jacksonrwoodard/HouseHealthMonitoring/Reports/Conceptual Design & Planning/Conceptual_Design_Draft.pdf

# Conceptual Design

Jackson Woodard, Dylan Robbins, Nathaniel Campbell, Luke Carson, Cole Cooper
Electrical and Computer Engineering Department Tennessee Technological University Cookeville, Tennessee
jrwoodard44@tntech.edu, dcrobbins42@tntech.edu, nmcampbell43@tntech.edu, lmcarson43@tntech.edu, cacopper44@tntech.edu
I. INTRODUCTION

Houses face many types of issues like gas leaks, fires, floods, and mold, which cause damage to the house leading to a decrease in value [1]–[3]. Unlike a smartphone or a modern car, current house constructions lack a mechanism to detect and monitor this information. This information, such as knowing if water damage has occurred, could improve the value of the house by proving that issues have not occurred or were taken care of quickly by the homeowner. In order to detect and monitor all of these problems, this project proposes a collection of sensors and a head unit, called Preserve Home Pro. The goal of the system is to measure, record, and display important active and historical data, giving a homeowner valuable information to help maintain and protect the value of their home. The Preserve Home Pro will be designed as a semi-permanent system that will last for up to thirty years. The system will also communicate information through a closed network without requiring internet. Combining these concepts, this project proposes an advanced solution to house health monitoring.
A current market for this type of system does not exist. Although there are several devices available to detect specific problems, none of this technology is integrated as a single system in houses today. Since many homes face issues with gas leaks, fires, floods, and mold, actively detecting these issues could be beneficial in preserving a home’s value [1]–[3]. In summary, The Preserve Home Pro will be designed as a semi-permanent system with multiple sensor modules that would detect and log these threats to a house, potentially increasing the value of a home.
This document is important in the design process because it will present general solutions based on the specifications and constraints stated in the project proposal. The document will also explain what each subsystem will do and give a more detailed description of the subsystem as a whole. Expanding on each subsystem will give the team an easier understanding of the problem and the proposed solution.
A. Specifications & Constraints

Stated below is a full list of the shall statements for the project placed in number order to be referenced (SC#) later in the document.

1) The Head unit shall know what sensor is sending data to it, the sensor’s location, and be able to differentiate from other sensors. This originated from the team supervisor.
2) The Head unit shall be able to display and log active and historical data from sensors. This originated from the project team and team supervisor.
3) Head unit shall be able to detect if the fire module temperature is at 176 degrees Fahrenheit or higher and display a warning [4]. This originated from the project team based on the fact of the drywall ignition level.
4) The Head unit shall be able to receive data from the water module to display a warning if water is present and the total water depth. This originated from the project team.
5) Head unit shall receive data from the gas module and follow OSHA standards for ammonia, propane, and carbon oxides (50 ppm, 1000 ppm, and 50 ppm respectively over an eight-hour window) [5]. This originated from the OSHA standards for the project.
6) Head unit shall be able to interpret, from the received data, that mold could form if the humidity levels exceed 50% and temperatures range between 55 degrees and 85 degrees Fahrenheit for a minimum of two days [6]. This originated from the project team based on the conditions in which mold can grow.
7) Head unit shall be able to receive the sensor name, number, data type, and raw data. This originated from the team supervisor.
8) Shall be a semi-permanent system that will last for up to thirty years. This originated from the team supervisor.
9) Shall have a backup power system that will allow the system to function in case of a primary power outage for up to two continuous weeks. This originated from both a standard and the team supervisor.
10) Shall fully function without having to regularly change batteries in sensors or head unit. This originated from all external stakeholders and the team supervisor.
11) Sensor modules shall not be placed in a way where they cannot wirelessly communicate with the system. This originated from the project team and broader implications.
12) Modules shall not be a distraction for a homeowner, and not be directly visible. This originated from all external stakeholders and the team supervisor.

13) The Water module shall be able to detect multiple water levels and determine if water is present. This originated from the project team.
14) The Mold module shall be able to detect the current temperatures and humidity levels in an area and send it to the head unit. This originated from the project team.
15) The Gas module shall be able to detect ammonia, propane, and carbon oxide. This originated from the project team and the insurance companies.
16) The Fire module shall be able to detect the temperature of the sensor and send the data to the head unit. This originated from the project team.
17) System shall not require an internet connection to work and communicate with the head unit and sensors. This originated from homeowners, insurance agencies, and the team supervisor.
18) Sensor communication shall send the sensor name, number, data type, and raw data to the head unit. This originated from the project team.
19) System shall not collect additional data that is not required for sensor functionality. This originated from all internal and external stakeholders and from broader implications.
20) System shall follow all IEEE Code of Ethics and common standards. This originated from the IEEE Code of Ethics.
B. Ethics & Broader Considerations
The design team will follow all National Fire Protection Agency 70: National Electrical Code (NFPA 70) and Occupational Safety and Health Administration (OSHA) procedures [SC5]. The team will also follow all government laws stated by the United States of America Government. The team will also follow all IEEE Code of Ethics and common standards, like resistor color codes, communications between devices, and design schematics [SC20]. The team will legally use all copyrights, patents, and licenses when necessary. The system will be designed to prevent all risk and harm when operated by the user and not be a distraction [SC12].

Due to the limited time and budget allocated to this project, there are multiple broader implications. Broader implications are the potential effects that the system could cause. Firstly, it may interfere with nearby radio frequency devices. Secondly, there is a risk of fire if any of the backup batteries become damaged. Additionally, false positives may be triggered due to sensor wear or damage. Also, one concern from the stakeholders is unnecessary data recording and sharing. It is essential that the system will not record conversations or cause any insecurities to the user [SC19]. Finally, given the installation process, it may be difficult to determine the level of effort required to maintain the sensors.

II. BLOCK DIAGRAM

The full detailed block diagram is pictured at the end of the document in figure 10.

A. Power System

The power system allows the Preserve Home Pro modules to function primarily on power from the house with a secondary backup battery in case of outages [SC9]. An uninterruptible power supply (UPS) will need to be implemented to allow the sensor modules to remain connected to the head unit. A charging system for the battery will also be needed so users do not have to change out batteries [SC10]. This power system will allow the Preserve Home Pro to operate for up to 30 years [SC8].


Fig. 1. Block Diagram of the Power System

B. Communication System

The Preserve Home Pro system uses wireless communication without an existing internet or WiFi connection in the house[SC17]. The transmission of the information from each module is used to record specific conditions of the house whether mold has grown, if water has accumulated, if gas is leaking or if a fire has occurred. Preserve Home Pro needs to be able to transmit the information from each module[SC11]. The information transmitted from each module should include the name of the sensor, the number of the sensor, the data type, and the sensor information[SC18]. The sent information should be small enough in data size to allow for minimal to no processing from the modules. The sent information should also allow for the head unit to discern each module from the others to allow for data processing of multiple inputs.

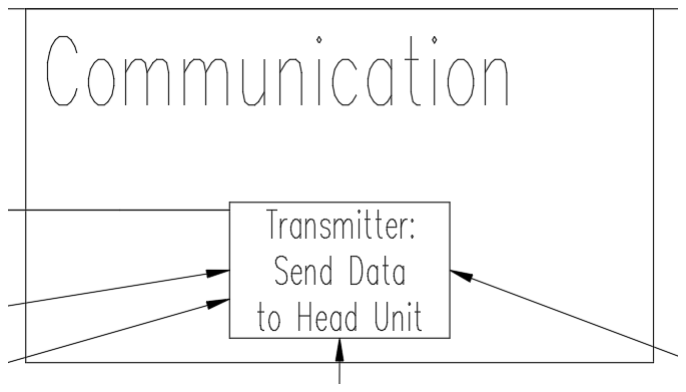
[picture p21: figure]

Fig. 2. Block Diagram for Communication System Transmitter

The head unit needs to be able to communicate with each of the modules. The reception of the information from each module is necessary for the proper functionality of the system. The received information will be routed through a receiver in the head unit. This receiver will be able to take information from the modules, like the name of the sensor, the sensor number, the data type, and the sensor information[SC1]. The information received can be used to determine if damage from mold, fire, water, or gas has occurred, and where the damages have occurred.

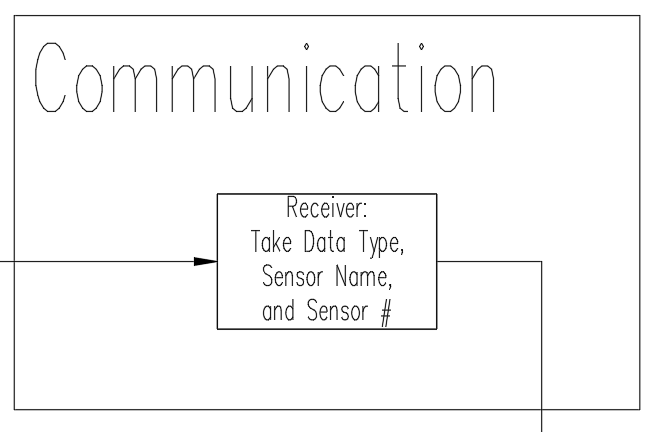
[picture p22: figure]

Fig. 3. Block Diagram for Communication System Receiver

C. System Modules
1) Head Unit: The head unit will be designed to display active and historical data [SC2]. The head unit will be able to determine the sensor name, number, data type, and raw data [SC7]. This information will be organized and interpreted to know what sensor is sending the data, and the sensor’s location, and be able to differentiate from other sensors [SC1]. The head unit will be able to detect if a temperature sensor has a temperature of 176 degrees Fahrenheit or higher and display a warning to the user [SC3]. It will also be able to detect if a water sensor has water present and the total depth of the water [SC4]. The head unit will also be able to determine if the data from the gas sensors are in the specified range according to OSHA standards for a set period of time [SC5]. Finally, the head unit will be able to determine if the data from the mold module is in the specified ranges for humidity and temperature and display a warning for potential mold growth if the conditions are present for a minimum of two days [SC6].

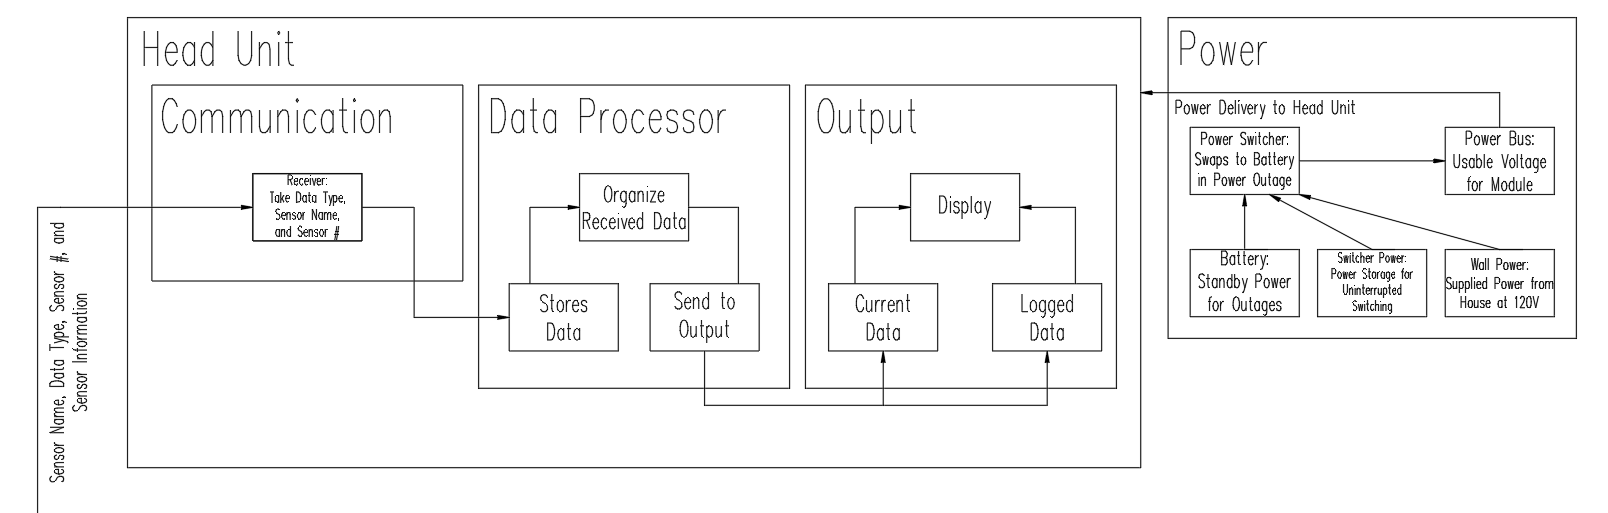
[picture p23: figure]

Fig. 4. Block Diagram of Head Unit

2) Mold Module: The mold module will be designed to have humidity and temperature sensors detecting their respective levels in a specified area and send the raw data, in the form of real numbers, back to the head unit [SC14]. These sensors will work together to determine if mold is likely to grow within the specified area. With the data the head unit receives from each sensor, the head unit will trigger a warning for potential mold growth if humidity levels exceed 50% and temperatures range between 55 to 85 degrees Fahrenheit for a minimum of two days [SC6].

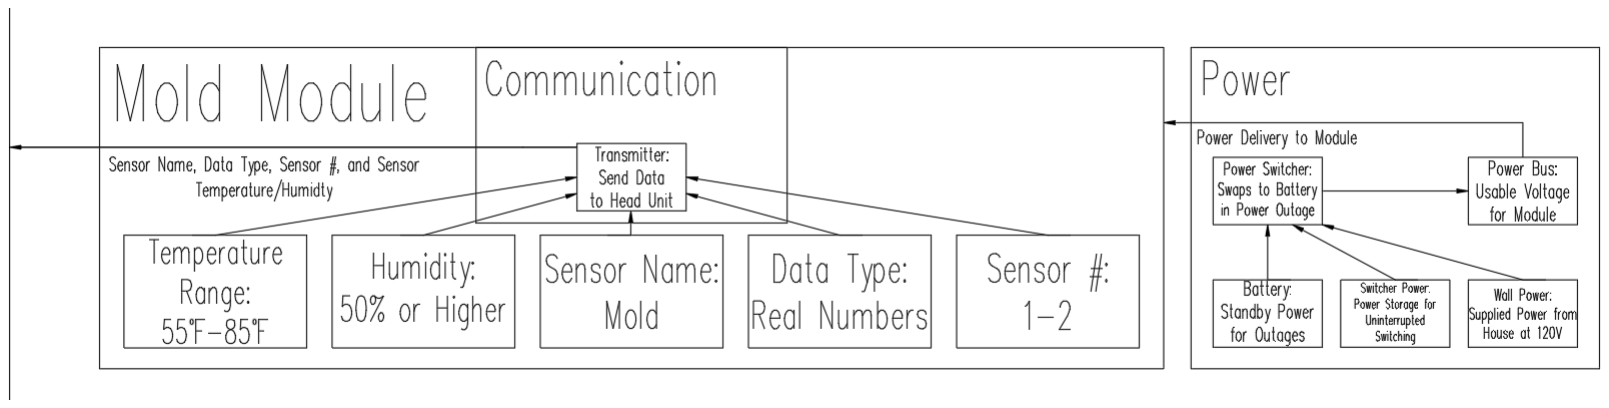
[picture p24: figure]

Fig. 5. Block Diagram of Mold Module

3) Gas Module: The gas module will detect three distinct gases – ammonia, carbon oxides, and propane - that tend to overlap in different sections of the house, such as smoke, septic, and natural gases [SC15]. The module is designed to detect these gases in specific areas of the house that are prone to leaks. Once the module detects the gases, built around OSHA standards, the data will be sent to the head unit for diagnosis [SC5].

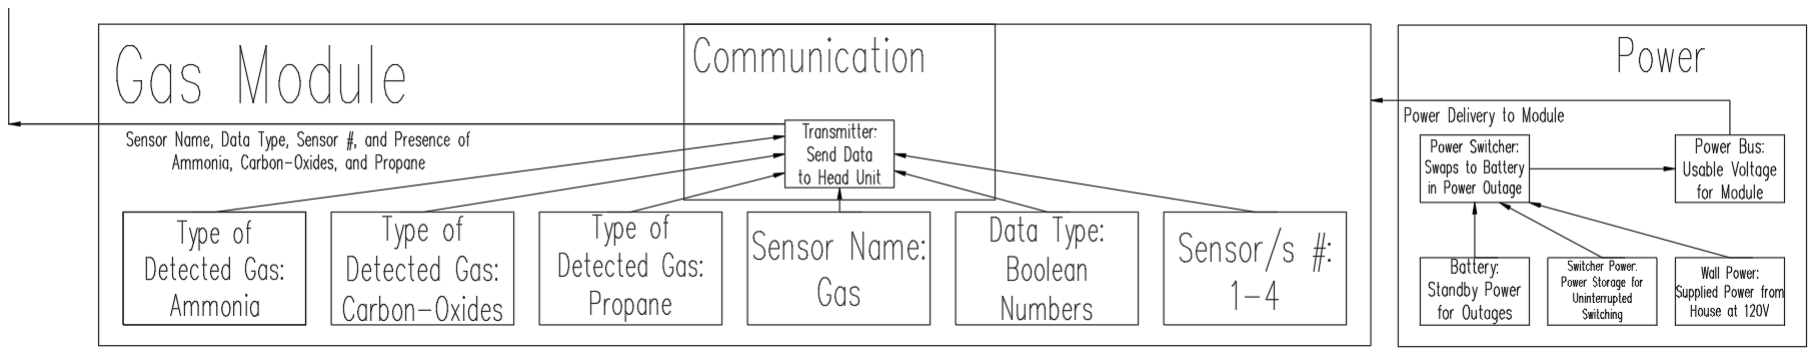
[picture p25: figure]

Fig. 6. Block Diagram of Gas Module

4) Fire Module: The fire module will be designed with sensors that will detect the current temperature and send the temperature data in the form of real numbers back to the head unit [SC16]. Once the data is received by the head unit, it will determine if the temperature is 176 degrees Fahrenheit or higher and display a warning message for the user to see [SC3].

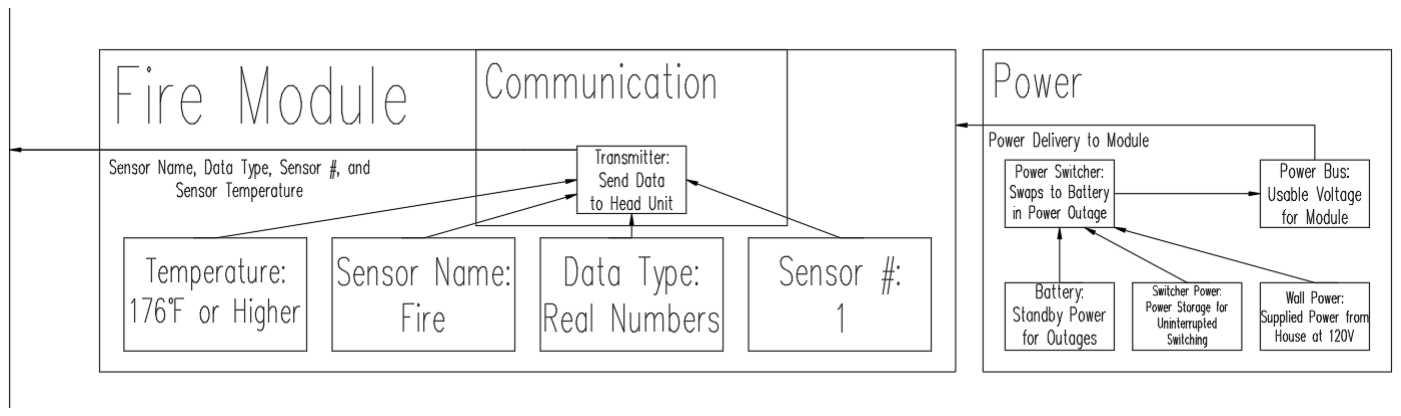
[picture p26: figure]

Fig. 7. Block Diagram of Fire Module

5) Water Module: The water module will have a sensor that can detect if water is present and the total depth of water[SC13]. It will then send this information back in the forms of real and Boolean values to the head unit so it can interpret and display the data [SC4].

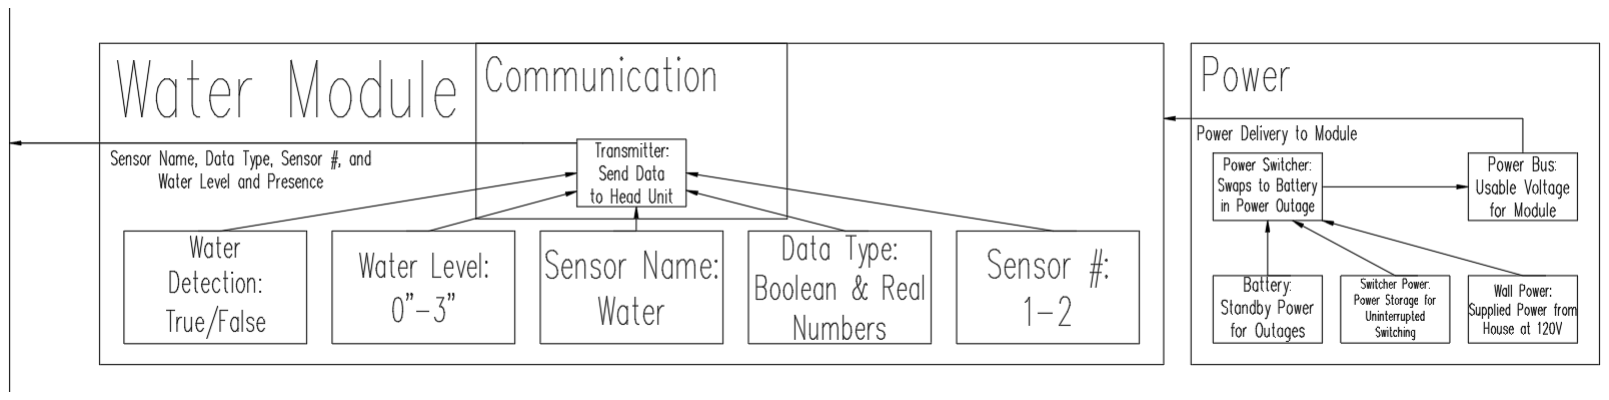
[picture p27: figure]

Fig. 8. Block Diagram of Water Module

III. TIMELINE
The expected timeline for the project is around one year. Figure 9 displays a Gantt chart that shows all of the team’s expected completion dates. The team plans to have everything built, utilized, and tested by May of 2024.

IV. CONCLUSION
In conclusion, the Preserve Home Pro project presents a solution to address various home health risks that can cause damage and deplete the value of a home such as gas leaks, fires, floods, and mold growth. The system will consist of multiple sensors and a head unit that will measure, record, and display historical and real-time data, providing homeowners with valuable information to help maintain and protect their homes. Each system module will be integrated into a semi-permanent system with a potential lifespan of up to thirty years. No internet connection will be required as the system will run within a closed network. This system is aimed to potentially help increase property value as well as give homeowners peace of mind that their home will remain in good health. This document serves as a foundational resource for the project, offering solutions aligned with project specifications and constraints and providing a detailed understanding of each subsystem’s role, marking a significant step towards revolutionizing home protection and preservation.

REFERENCES

[1] Insurance Information Institute, “Facts + statistics: Homeowners
and | renters | insurance,” | III, | https://www.iii.org/fact-statistic/
facts-statistics-homeowners-and-renters-insurance#:∼:text=In% 202021%2C%205.3%20percent%20of%20insured%20homes% 20experienced%20a%20claim,with%206.3%20percent%20in% 202020(accessedSep.17,2023).
[2] R. Peysakhovich, “47 mold statistics: Black Mold deaths per year,” Professional Commercial Cleaning Services by Onedesk, https://www.getonedesk.com/mold-statistics (accessed Sep. 17, 2023).
[3] M. Ahrens, Fire safety in the United States since 1980 - NFPA, https://www.nfpa.org/∼/media/Files/News%20and%20Research/Fire%20statistics%20and%20reports/US%20Fire%20Problem/
osNFPAEcosystemFireSafetyReport2021.ashx | (accessed | Sep. | 17,
2023).
[4] N. P. Team, “At what temperature will drywall ignite?,” NCERT POINT, https://www.ncertpoint.com/2022/01/at-what-temperature-willdrywall-ignite.html (accessed Oct. 3, 2023).
[5] OSHA, | “1910.1000 | table | Z-1 | - | Table | Z-1 | lim-
its | for | Air | Contaminants,” | Occupational | Safety | and
Health | Administration, | https://www.osha.gov/laws-
regs/regulations/standardnumber/1910/1910.1000TABLEZ1 | (accessed
Oct. 3, 2023).
[6] Adam, “Mold Chart for Temperature and Humidity Monitors,” Stetten home services, https://energyhandyman.com/knowledge-library/moldchart-for-temperature-and-humidity-monitors/ (accessed Sep. 28, 2023).

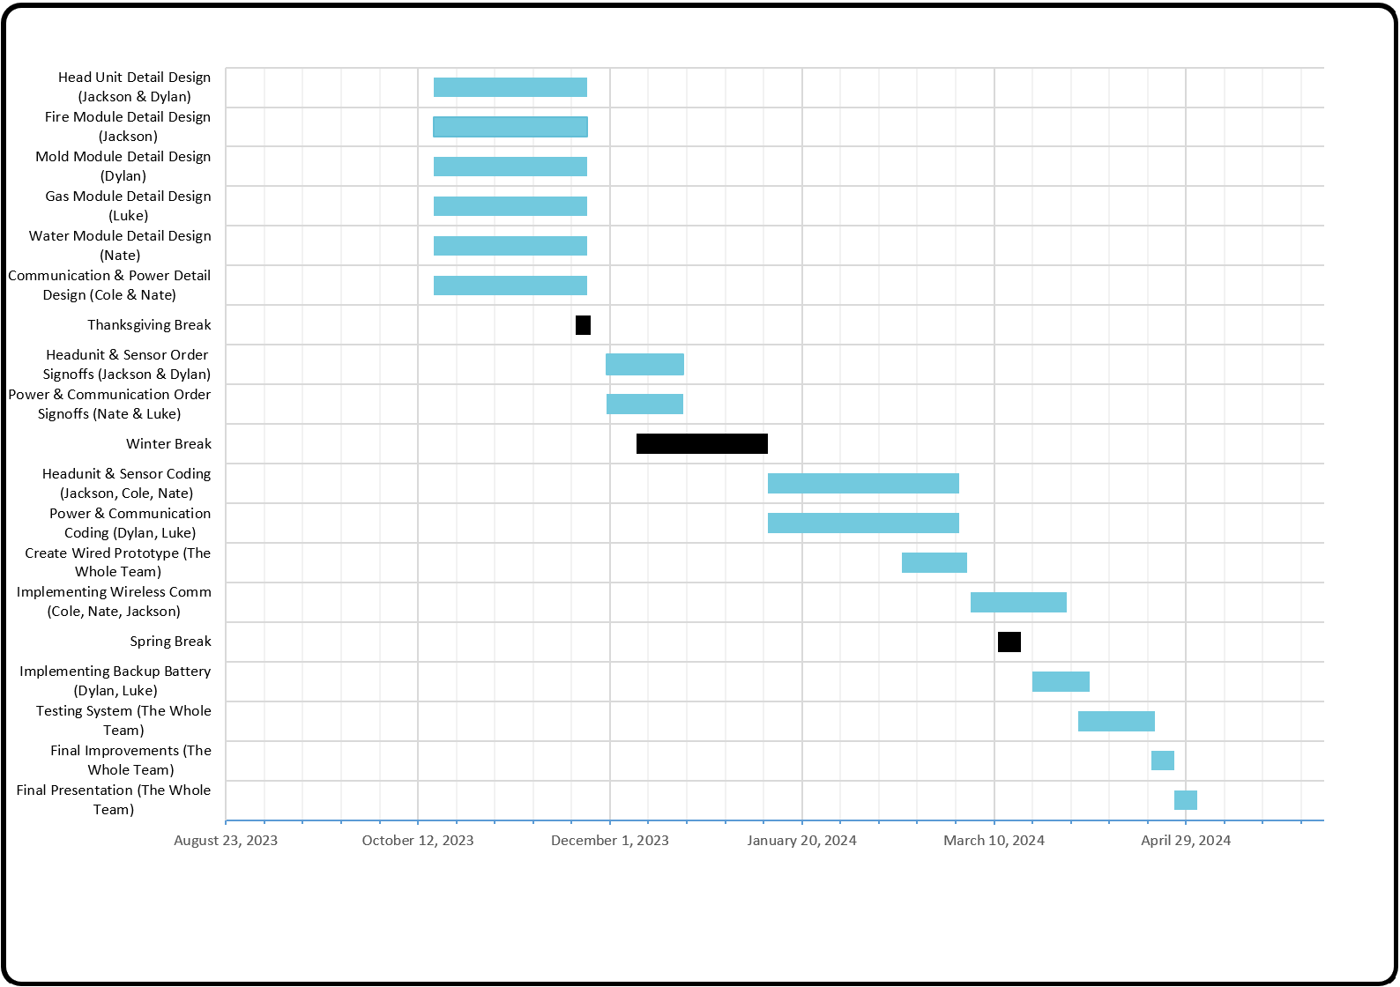
[picture p28: figure]

Fig. 9. Expected Timeline

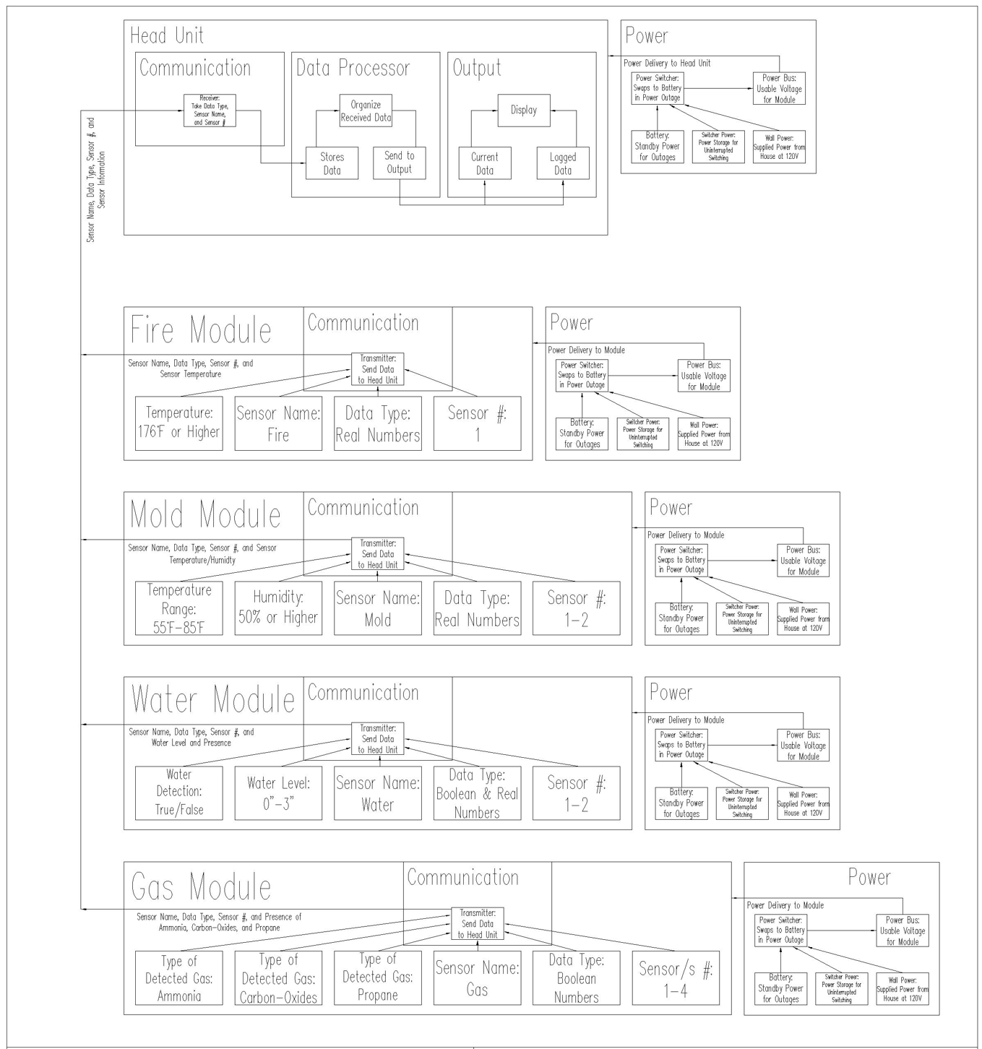
[picture p29: figure]

Fig. 10. Detailed Block Diagram
