jacksonrwoodard/HouseHealthMonitoring/Documentation/Meeting Minutes/Minutes - 2023-10-12.md

Opening
The team meeting of Capstone I Team 4 was held at 12:00 PM on October 12, 2023 in Brown Hall in room 408.

Present
Nate Campbell, Team Member
Luke Carson, Team Member
Cole Cooper, Secretary
Dylan Robbins, Team Member
Jackson Woodard, Team Lead
Jesse Roberts, Sponsor

Absent
All Present

Approval of Agenda
The agenda was unanimously approved by the team.

Approval of Minutes
The meeting minutes were unanimously approved by the team.

Business From Previous Meeting
The final edits of the project proposal corrections and the initial conceptual design submission.

New Business 
No new business was started from this meeting. 

Additions to the Agenda
Additional information for the specifications and constraints is needed before the project proposal’s submission. 
Extra text for the flow chart’s arrows for ease of reading also needs to be added. 
Some small clarifications on how the flow chart works in the paper was requested, 
however the request came from a skimming of the paper and the team feels that this request has been met. 

Agenda for Next Meeting
Initial planning for the detailed design submissions. 

Adjournment 
Meeting was adjourned at 3:00 PM by Jackson Woodard. With planning of meeting again on October 19, 2023 at 12:00 PM in Brown 408.

Minutes Submitted by: Cole Cooper
Approved by: Jackson Woodard
