jacksonrwoodard/HouseHealthMonitoring/Documentation/Meeting Minutes/Minutes - 2023-10-5.md

Opening
The team meeting of Capstone I Team 4 was held at 12:00 PM on October 5, 2023 in
Brown Hall in room 408.
Present
Nate Campbell, Team Member
Luke Carson, Team Member
Cole Cooper, Secretary
Dylan Robbins, Team Member
Jackson Woodard, Team Lead
Jesse Roberts, Sponsor
Absent
All Present
Approval of Agenda
The agenda was unanimously approved by the team.
Approval of Minutes
The meeting minutes were unanimously approved by the team.
Business From Previous Meeting
Editing of the flow chart, conceptual design paper, and project proposal were done
during this meeting.
New Business
No new business was started from this meeting.
Additions to the Agenda
A decent amount of discussion around making sure the project proposal follows the
supplied rubric was done. We ended up dividing the workload between each member in
order to speed up the editing process. After each individual section was completed, the
team went through and reviewed the edited information to ensure the goals of the rubric
were properly met this time around. This process was then repeated for the conceptual
design and the conceptual design block diagram.
Agenda for Next Meeting
Final edits for the conceptual design and block diagram will be covered next meeting.
Adjournment
Meeting was adjourned at 3:00 PM by Jackson Woodard. With planning of meeting
again on October 12, 2023 at 12:00 PM.
Minutes Submitted by: Cole Cooper
Approved by: Jackson Woodard
