jacksonrwoodard/HouseHealthMonitoring/Documentation/Electrical/Schematics/Sources/Communication.pdf

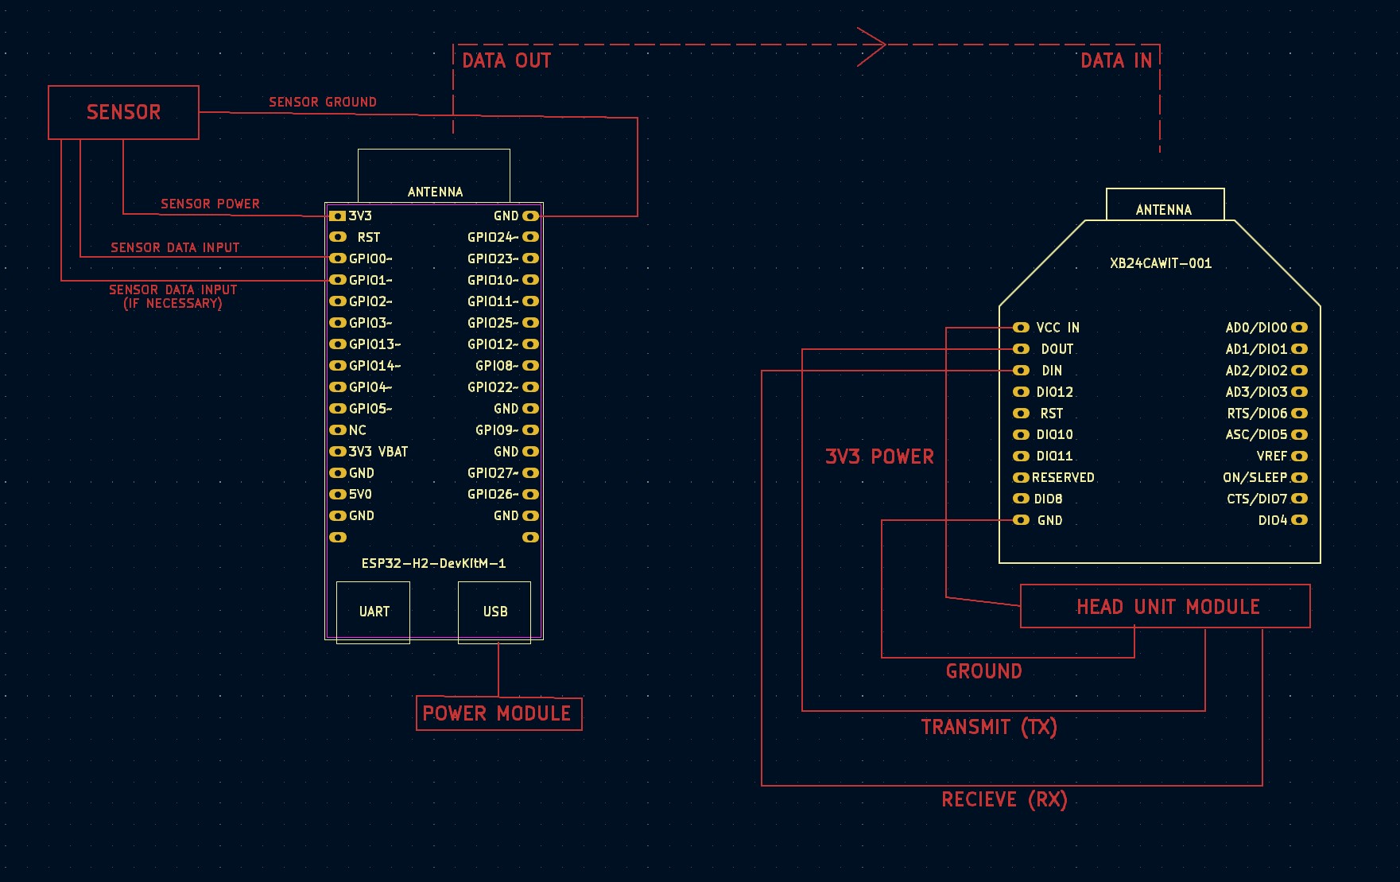
[picture p30: page 1]
