jacksonrwoodard/HouseHealthMonitoring/Documentation/Electrical/Schematics/Sources/Fire.pdf

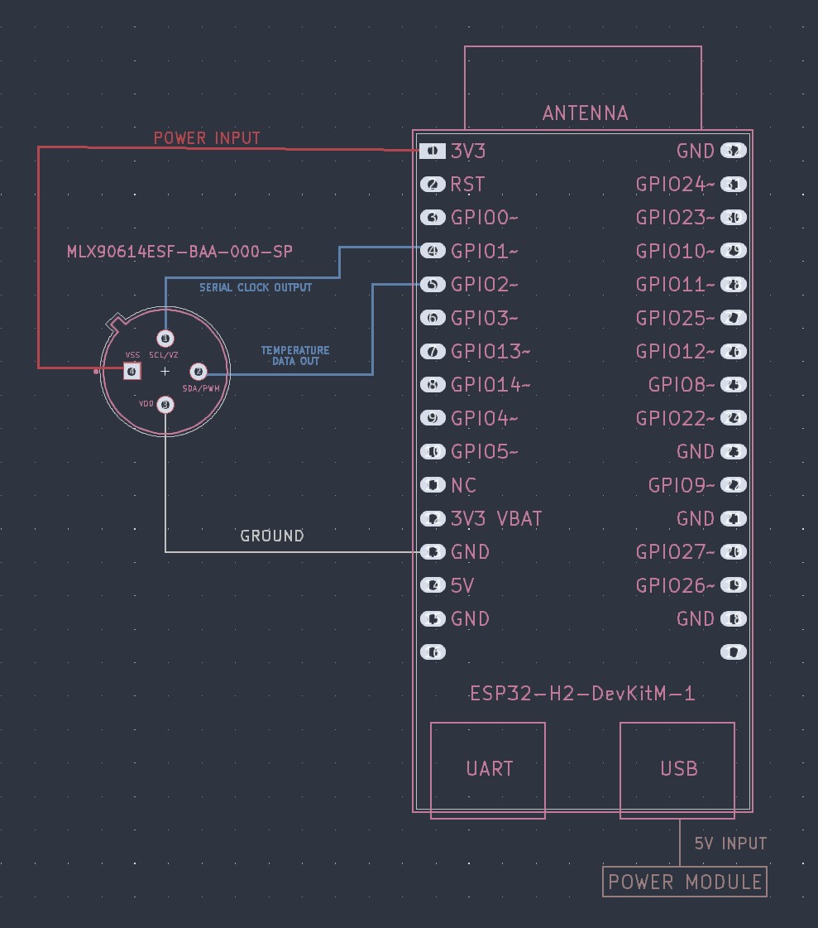
[picture p31: page 1]
