jacksonrwoodard/HouseHealthMonitoring/Documentation/Electrical/Schematics/Sources/Flood.pdf

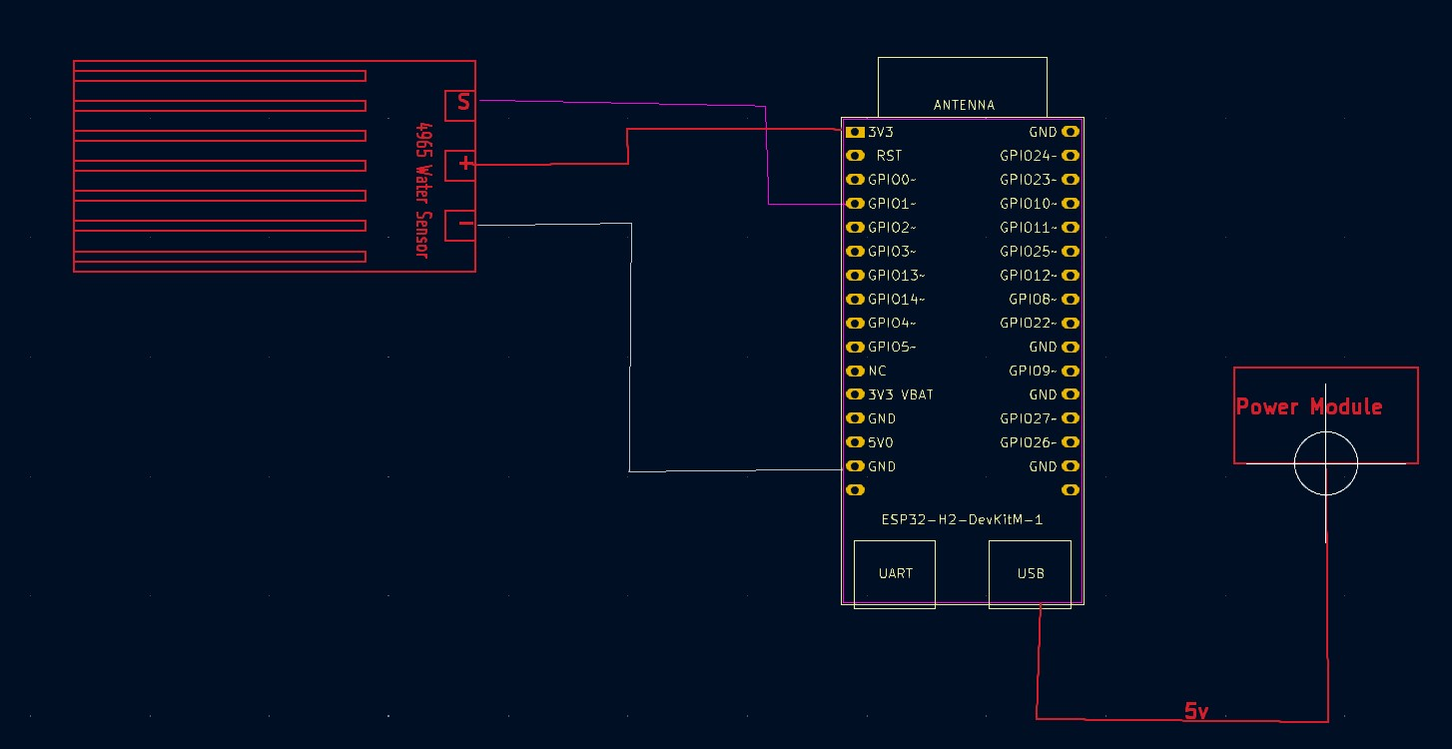
[picture p32: page 1]
