jacksonrwoodard/HouseHealthMonitoring/Documentation/Electrical/Schematics/Sources/Gas.pdf

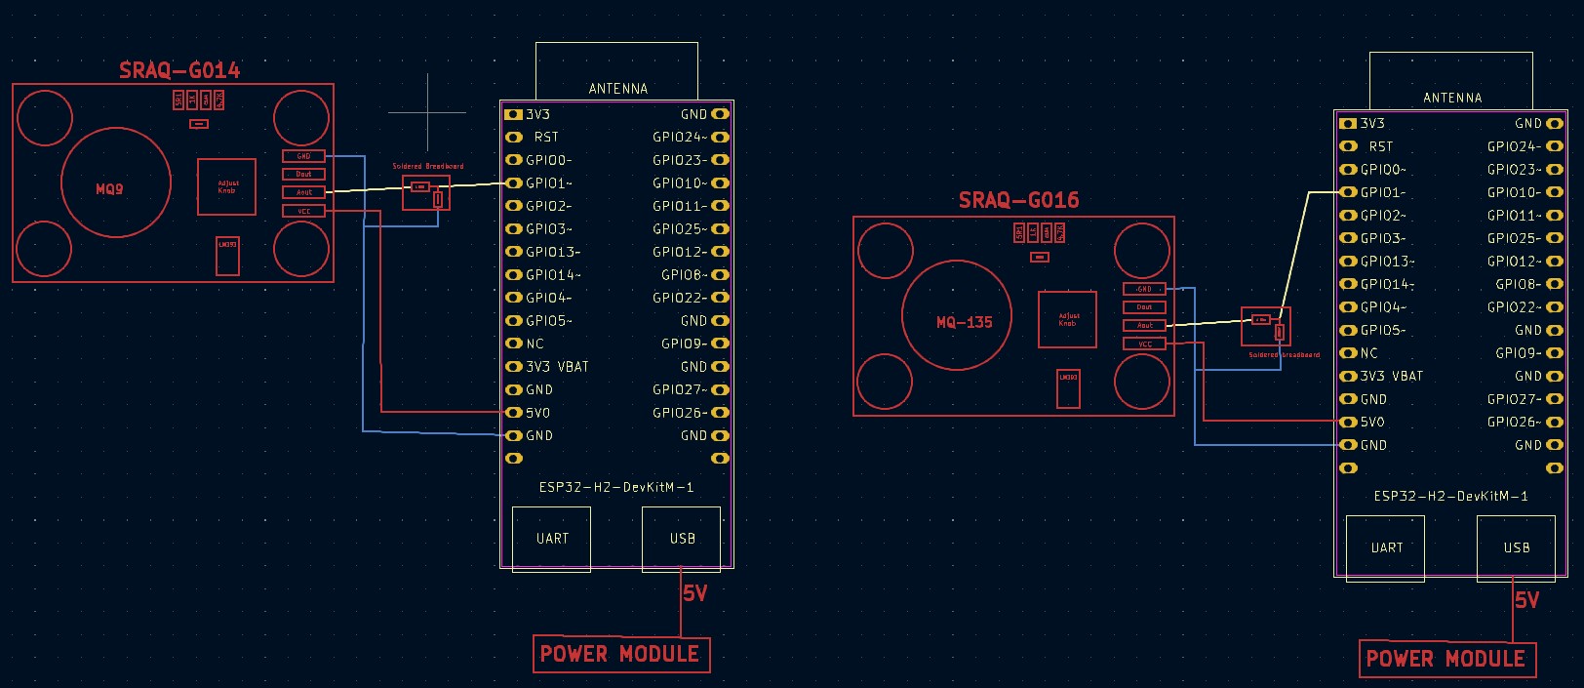
[picture p33: figure]
