jacksonrwoodard/HouseHealthMonitoring/Documentation/Electrical/Schematics/Sources/Head_Unit.pdf

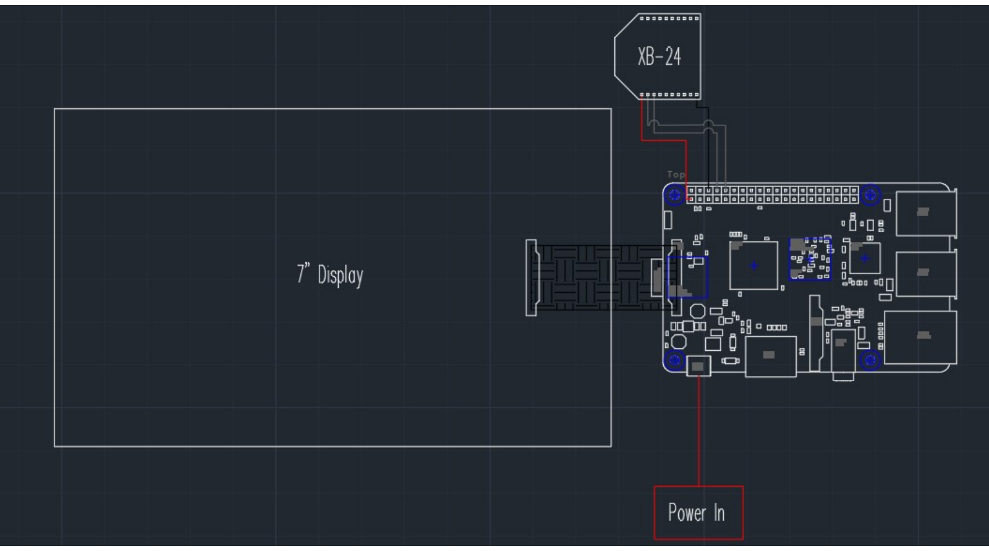
[picture p34: page 1]
