jacksonrwoodard/HouseHealthMonitoring/Documentation/Electrical/Schematics/Sources/Mold.pdf

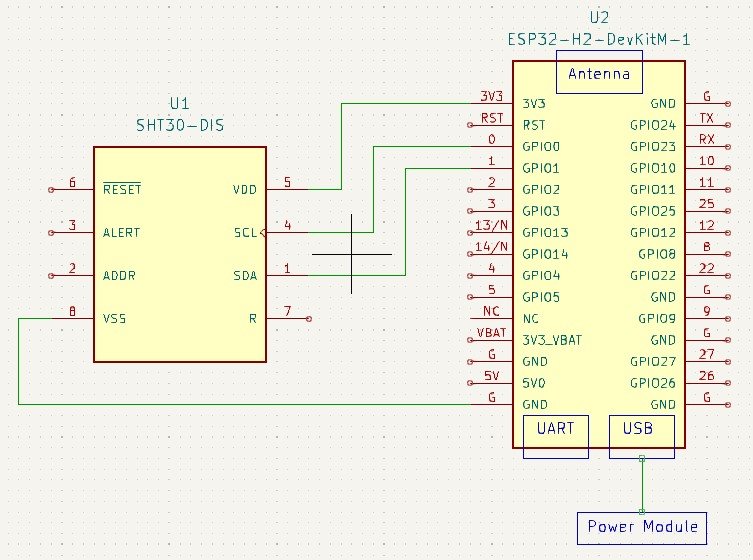
[picture p35: figure]
