jacksonrwoodard/HouseHealthMonitoring/Documentation/Electrical/Schematics/Sources/Power.pdf

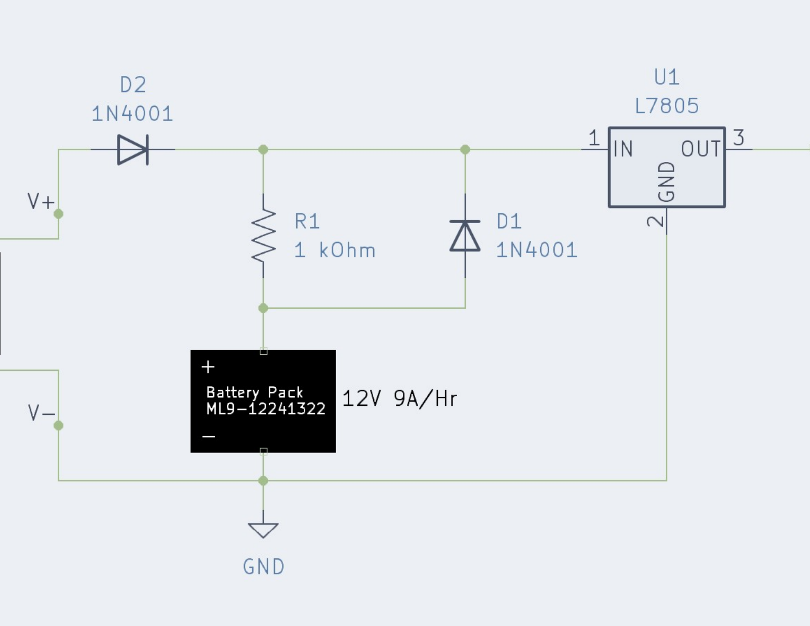
[picture p36: page 1]
