jacksonrwoodard/HouseHealthMonitoring/Documentation/Images/Communication/Reciever.png

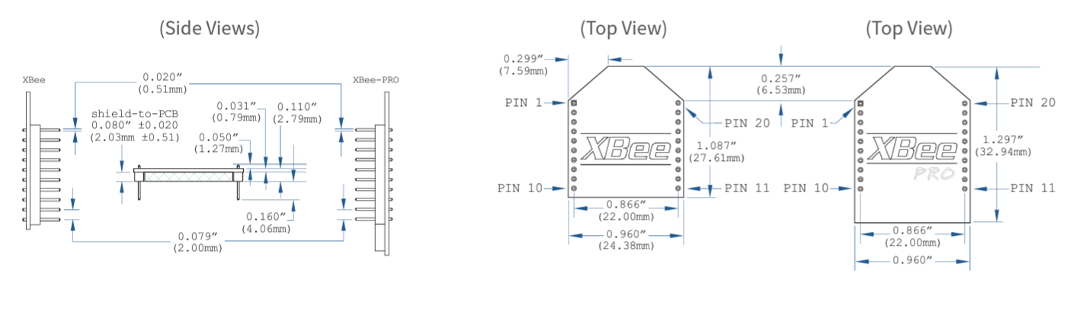
Documentation/Images/Communication/Reciever.png
