jacksonrwoodard/HouseHealthMonitoring/Documentation/Images/HeadUnit/Head_Unit_Display.PNG

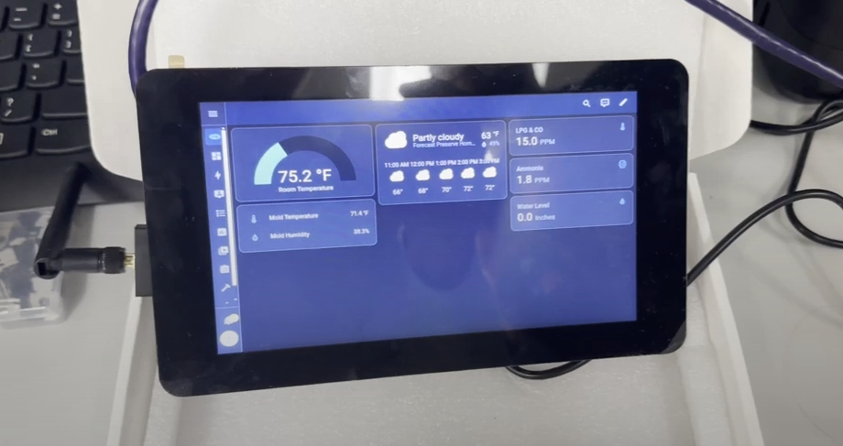
Documentation/Images/HeadUnit/Head_Unit_Display.PNG
