jacksonrwoodard/HouseHealthMonitoring/Documentation/Images/HeadUnit/Head_Unit_MCU.PNG

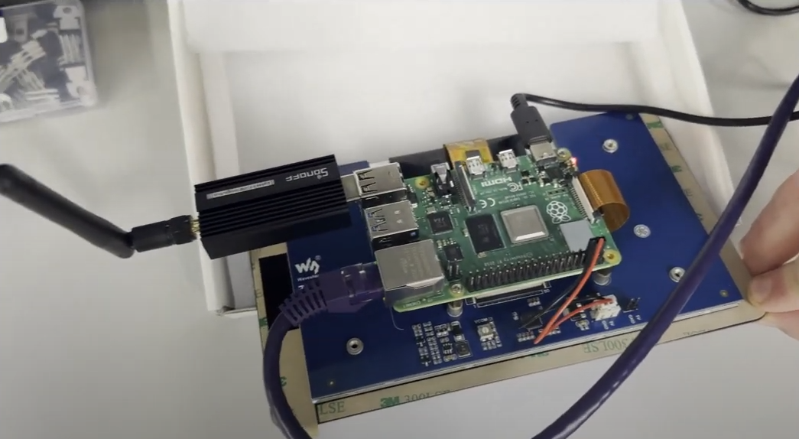
Documentation/Images/HeadUnit/Head_Unit_MCU.PNG
