jacksonrwoodard/HouseHealthMonitoring/Documentation/Images/Mold/Mold_Sensor.jpg

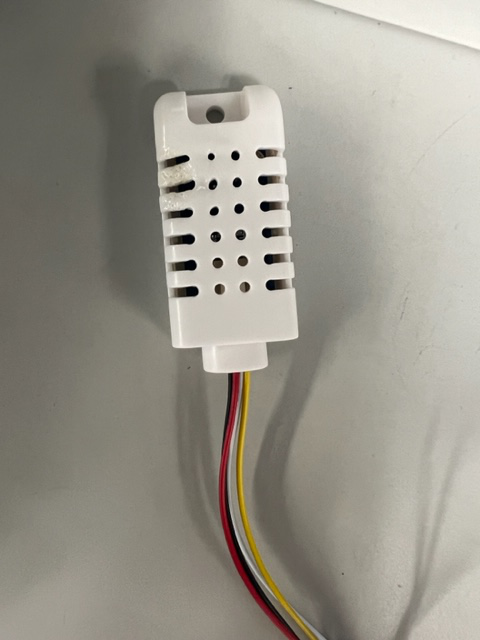
Documentation/Images/Mold/Mold_Sensor.jpg
