jacksonrwoodard/HouseHealthMonitoring/Documentation/Images/Communication/Communication_Test_50ft.png

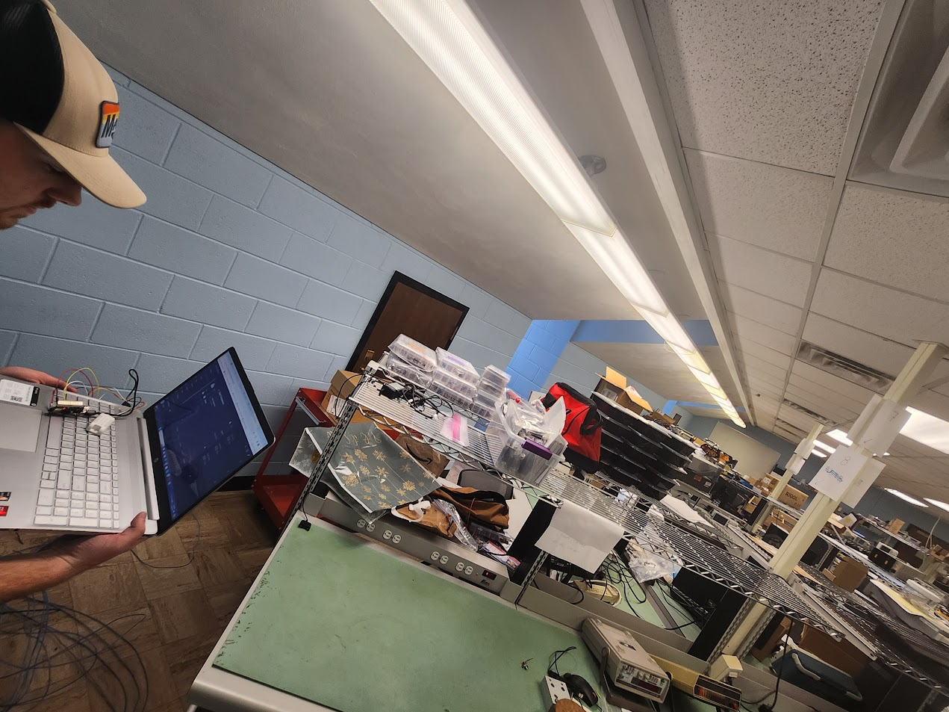
Documentation/Images/Communication/Communication_Test_50ft.png
