jacksonrwoodard/HouseHealthMonitoring/Documentation/Images/Communication/Communication_Test_100ft_with_walls.png

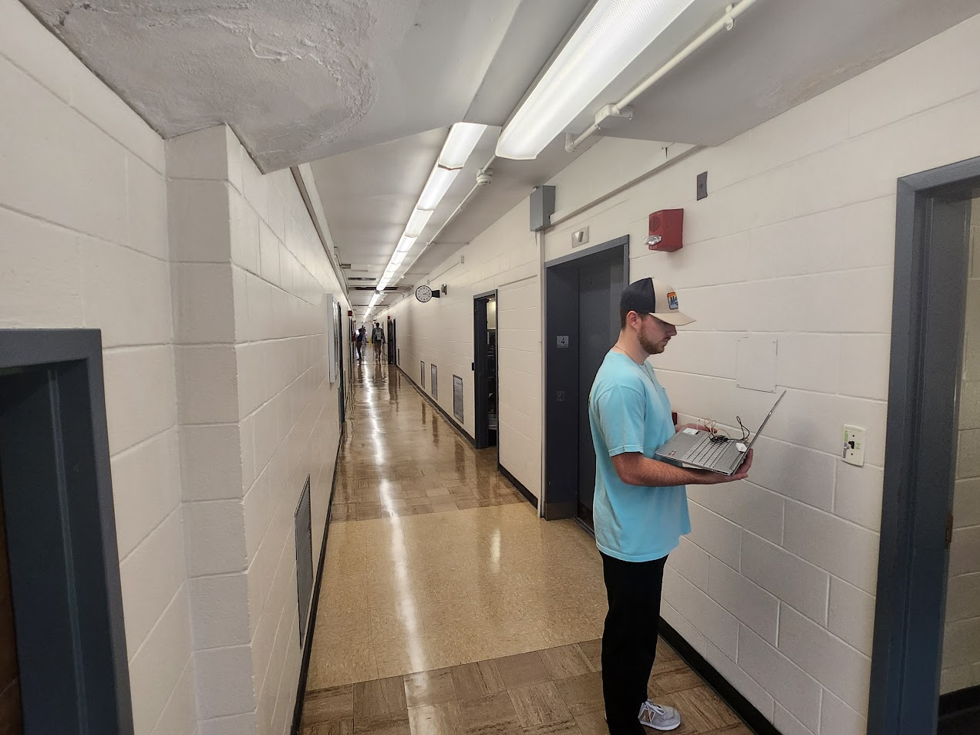
Documentation/Images/Communication/Communication_Test_100ft_with_walls.png
