jacksonrwoodard/HouseHealthMonitoring/Documentation/Images/Fire/Fire_Test_176_Degree.jpg

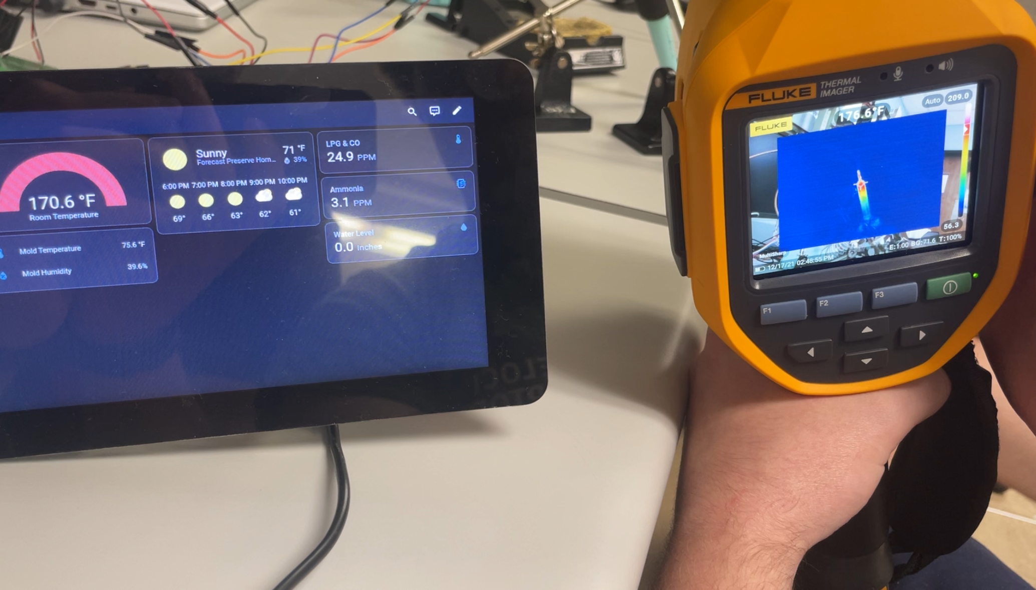
Documentation/Images/Fire/Fire_Test_176_Degree.jpg
