jacksonrwoodard/HouseHealthMonitoring/Documentation/Images/Gas/Gas_Test_Airvent.png

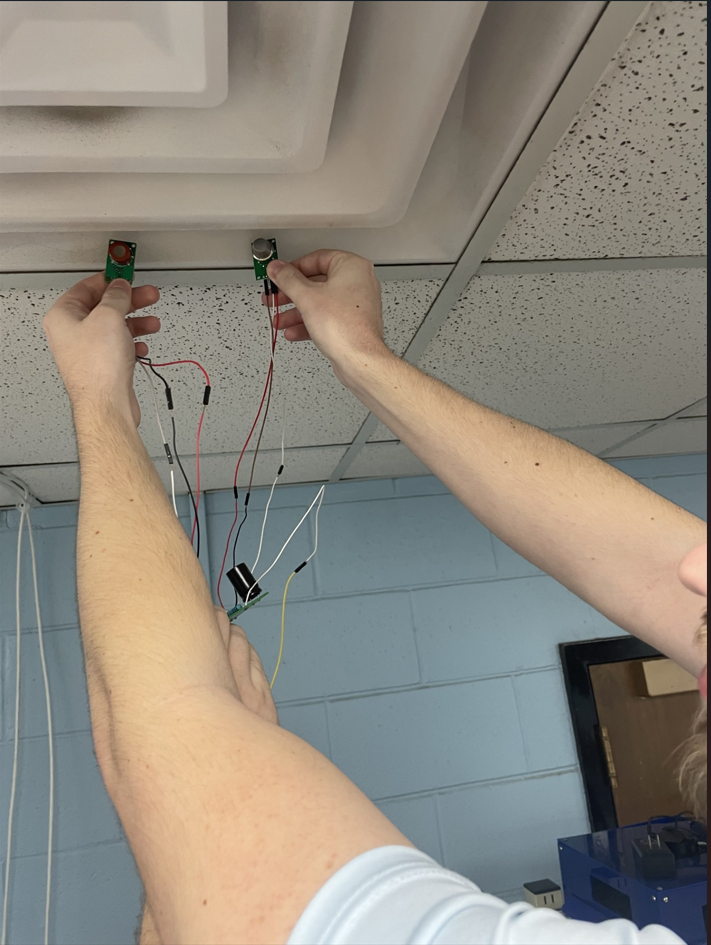
Documentation/Images/Gas/Gas_Test_Airvent.png
