jacksonrwoodard/HouseHealthMonitoring/Documentation/Images/Gas/Gas_Test_Dust.png

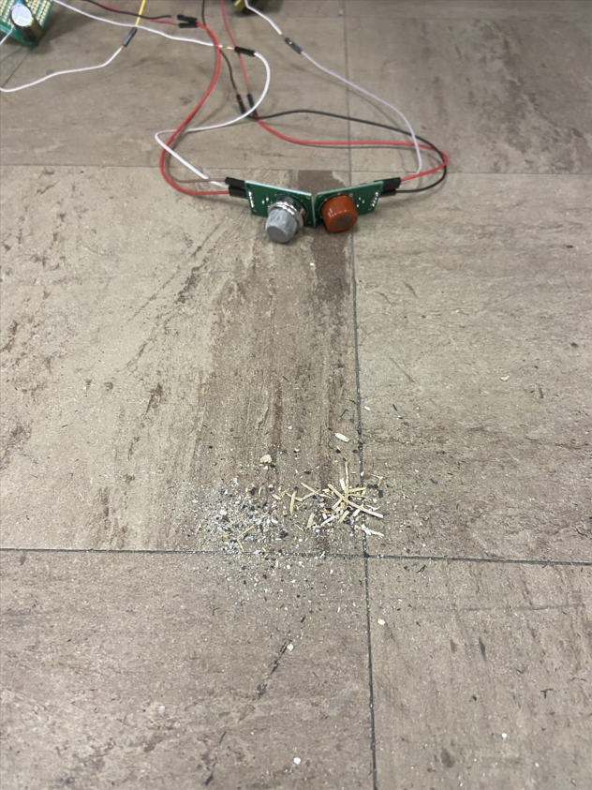
Documentation/Images/Gas/Gas_Test_Dust.png
