jacksonrwoodard/HouseHealthMonitoring/Documentation/Images/Power/Power_Plugged_In_Test.png

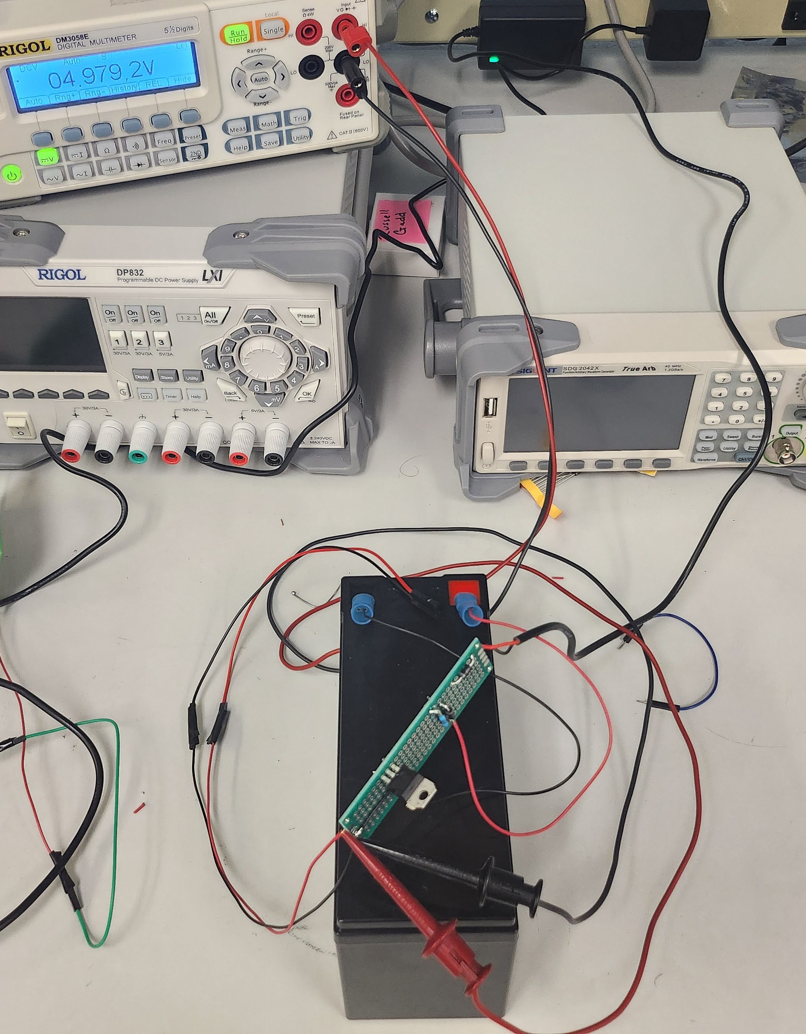
Documentation/Images/Power/Power_Plugged_In_Test.png
