jacksonrwoodard/HouseHealthMonitoring/Documentation/Images/Power/Power_Unplugged_Test.png

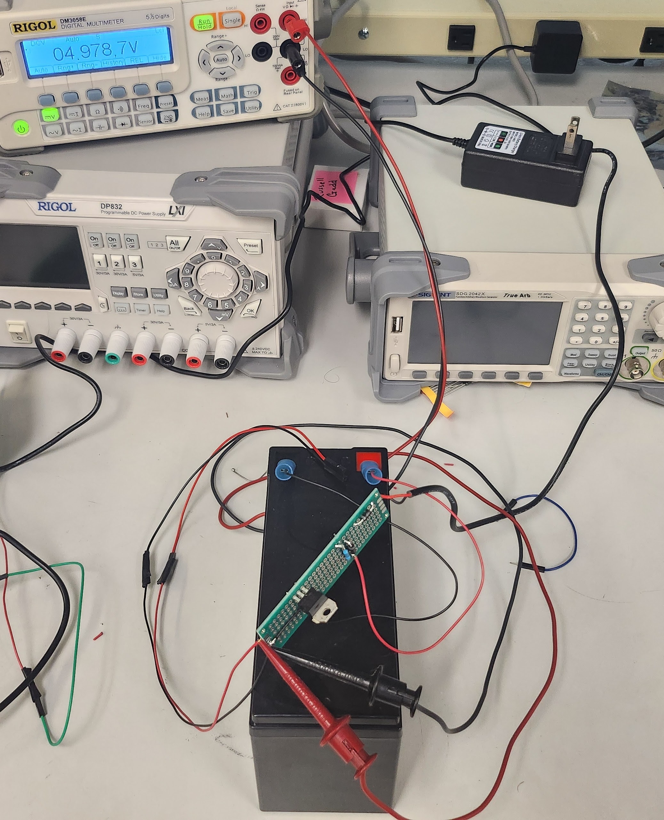
Documentation/Images/Power/Power_Unplugged_Test.png
